jarpoole/etherweasel/software/results/active_mode_throughputs.png

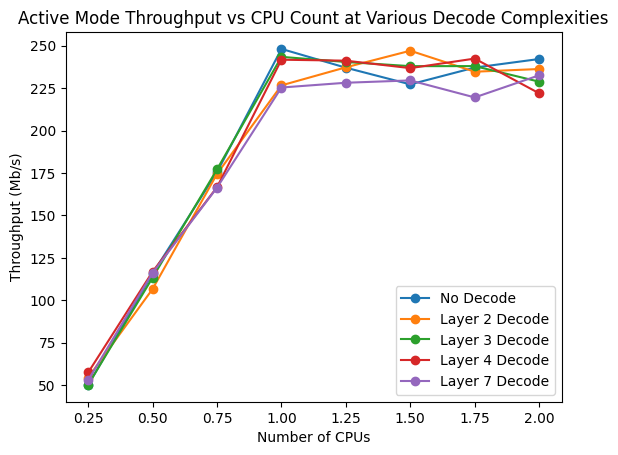
software/results/active_mode_throughputs.png
