jarpoole/etherweasel/software/results/active_vs_passive_norm_error_rate.png

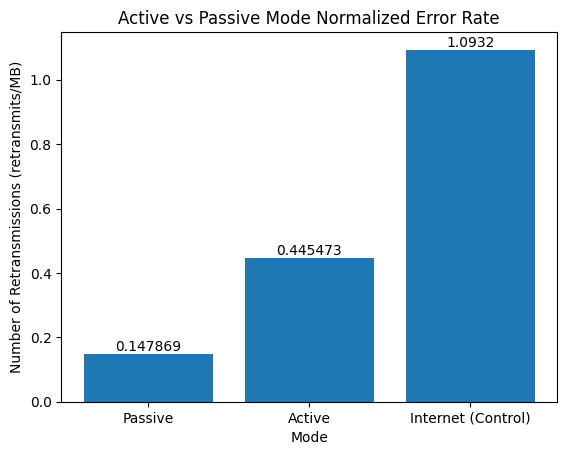
software/results/active_vs_passive_norm_error_rate.png
