jarpoole/etherweasel/software/results/active_vs_passive_rtt.png

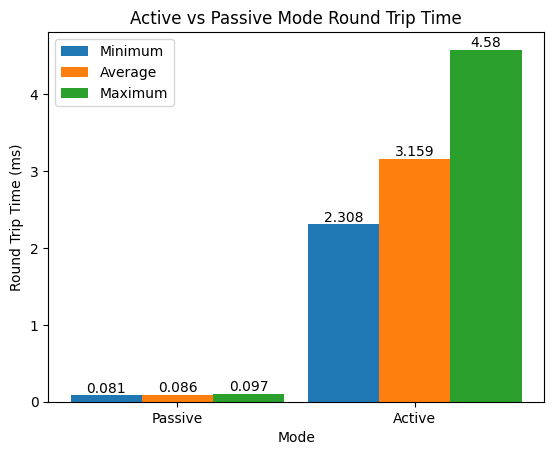
software/results/active_vs_passive_rtt.png
