jarpoole/etherweasel/software/results/active_vs_passive_throughputs.png

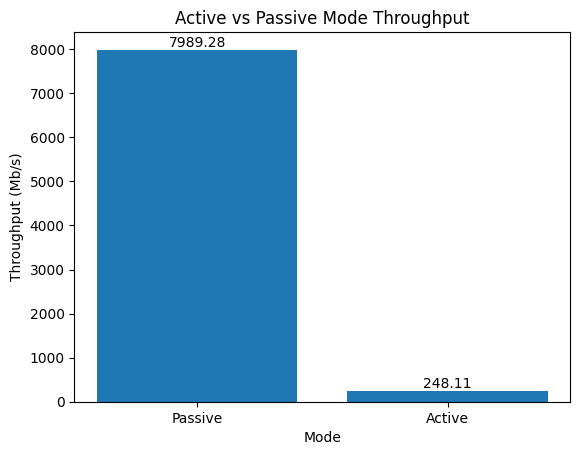
software/results/active_vs_passive_throughputs.png
