jarpoole/etherweasel/software/results/real_world_throughputs.png

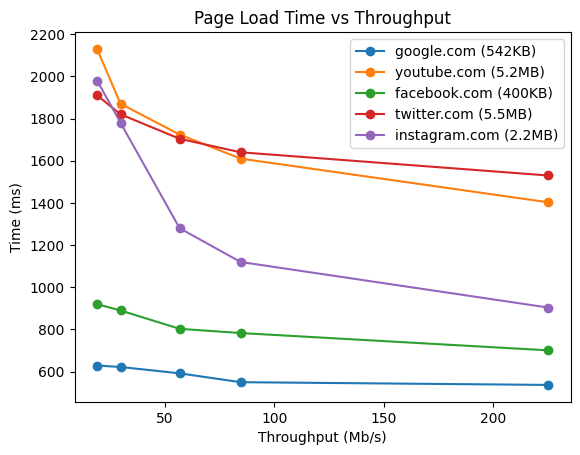
software/results/real_world_throughputs.png
